TiagoJustino/ritchie/photon/unknownsong.h

#ifndef UNKOWN_SONG_H
#define UNKOWN_SONG_H
#include "pitches.h"

int unknownSongMelodyLength = 9;

int unknownSongMelody[] = {
  NOTE_C4, NOTE_G3,NOTE_G3, NOTE_A3, NOTE_G3, REST, NOTE_B3, NOTE_C4, REST
};

float unknownSongNoteDurations[] = {
  8,16,16,8,8,8,8,8,8
};

#endif
