TiagoJustino/ritchie/photon/eyeofthetiger.h

#ifndef EYE_OF_THE_TIGER_H
#define EYE_OF_THE_TIGER_H
#include "pitches.h"

int eyeMelodyLength = 14;

int eyeMelody[] = {
  NOTE_B5,
  REST,
  NOTE_B5,
  NOTE_A5,
  NOTE_B5,
  REST,
  NOTE_B5,
  NOTE_A5,
  NOTE_B5,
  REST,
  NOTE_B5,
  NOTE_A5,
  NOTE_G5,
  NOTE_A5
};

float eyeNoteDurations[] = {
  6,
  3,
  6,
  6,
  6,
  3,
  6,
  6,
  6,
  3,
  6,
  6,
  1.5,
  1.5
};

#endif
